Charading/Shego75HE/shego75_breadboard/config.h

/* config.h - keyboard configuration for shego75_v1 */
#pragma once

// Encoder switch (optional - not part of standard encoder config)
#ifndef ENCODER_SW_PIN
#define ENCODER_SW_PIN GP10
#endif
// #define ENCODER_DIRECTION_FLIP
